darkavenger75/mk312lite/images/mk312lite_case2.jpg

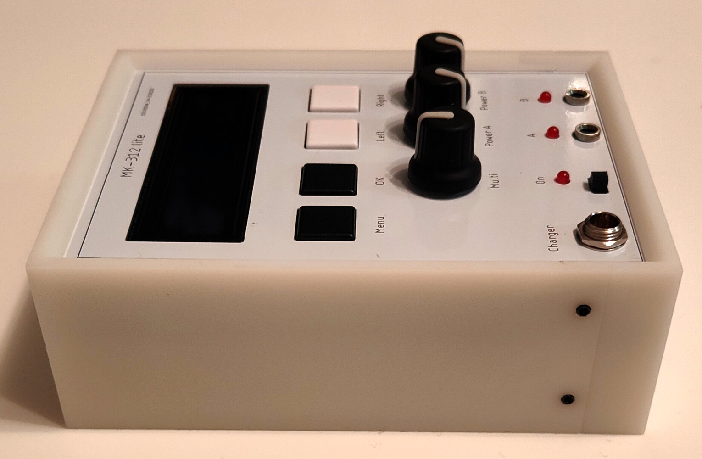
images/mk312lite_case2.jpg
