darkavenger75/mk312lite/images/mk312lite_side.jpg

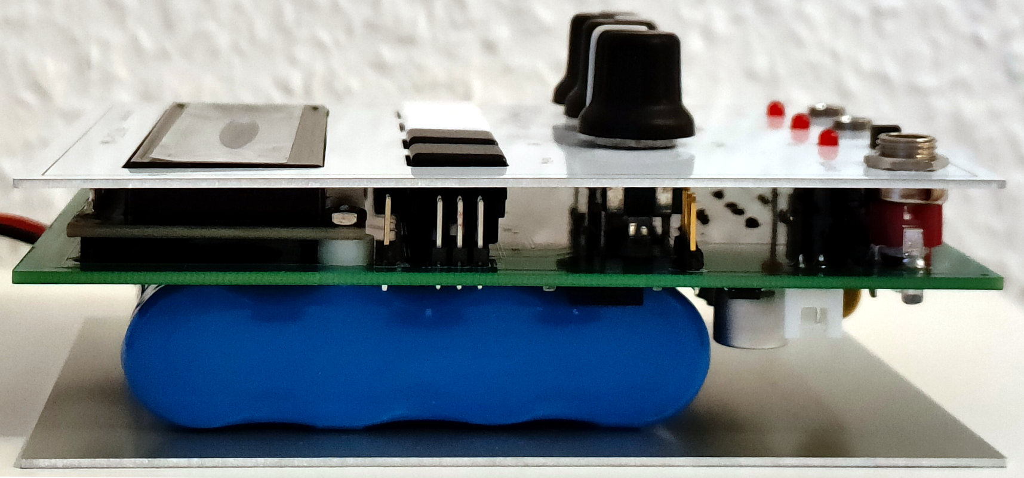
images/mk312lite_side.jpg
